TravisBumgarner/pixels64/my_displays/src/main.py

from collections import OrderedDict

# from display_images import display_images
# from chat_gpt import (
#     display_dual_chase,
# )
# from chat_gpt2 import (
#     display_voronoi_ripple,
#     display_spiral_scan,
#     display_diagonal_wave,
#     display_hilbert_wave,
#     display_jpeg_zigzag,
#     display_morton_weave,
# )
# from display_gradient_squares import display_gradient_squares
# from display_zigzag import display_zigzag
from display_christmas_squares import display_gradient_squares


displays_to_run = OrderedDict(
    {
        "display_gradient_squares": display_gradient_squares,
        # "dual_chase": display_dual_chase,
        # "voronoi_ripple": display_voronoi_ripple,
        # "spiral_scan": display_spiral_scan,
        # "diagonal_wave": display_diagonal_wave,
        # "hilbert_wave": display_hilbert_wave,
        # "jpeg_zigzag": display_jpeg_zigzag,
        # "morton_weave": display_morton_weave,
        # "gradient_squares": display_gradient_squares,
        # "zigzag": display_zigzag,
    }
)

LAST_DISPLAY_FILE = "last_display.txt"


def save_last_display(name):
    with open(LAST_DISPLAY_FILE, "w") as f:
        f.write(name)


def get_last_display():
    try:
        with open(LAST_DISPLAY_FILE, "r") as f:
            return f.read().strip()
    except:
        return None


def get_next_display(current):
    displays = list(displays_to_run.keys())
    if not current or current not in displays:
        return displays[0]
    current_idx = displays.index(current)
    next_idx = (current_idx + 1) % len(displays)
    return displays[next_idx]


def main():
    # Power cycle device to get next display
    last_display = get_last_display()
    display_name = get_next_display(last_display)

    print(f"Displaying {display_name}")
    save_last_display(display_name)

    displays_to_run[display_name]()


if __name__ == "__main__":
    main()
