TravisBumgarner/pixels64/my_displays/src/config.py

# First display
LOOKUP = [
    63,
    62,
    61,
    60,
    47,
    46,
    45,
    44,
    59,
    58,
    57,
    56,
    43,
    42,
    41,
    40,
    55,
    54,
    53,
    52,
    39,
    38,
    37,
    36,
    51,
    50,
    49,
    48,
    35,
    34,
    33,
    32,
    15,
    14,
    13,
    12,
    31,
    30,
    29,
    28,
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
]


#  New Display
# LOOKUP = [
#     0,
#     1,
#     2,
#     3,
#     16,
#     17,
#     18,
#     19,
#     4,
#     5,
#     6,
#     7,
#     20,
#     21,
#     22,
#     23,
#     8,
#     9,
#     10,
#     11,
#     24,
#     25,
#     26,
#     27,
#     12,
#     13,
#     14,
#     15,
#     28,
#     29,
#     30,
#     31,
#     32,
#     33,
#     34,
#     35,
#     48,
#     49,
#     50,
#     51,
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
# ]

# 2D mapping for easier coordinate-based access (8x8 grid)
GRID_SIZE = 8
LOOKUP_2D = [
    LOOKUP[row * GRID_SIZE : (row + 1) * GRID_SIZE] for row in range(GRID_SIZE)
]


def get_led_index(row, col):
    """Helper function to get LED index from 2D coordinates (0-7, 0-7)"""
    if 0 <= row < 8 and 0 <= col < 8:
        return LOOKUP_2D[row][col]
    return None
